Natologic/metalTravelPad/img/IMG_0876.jpg

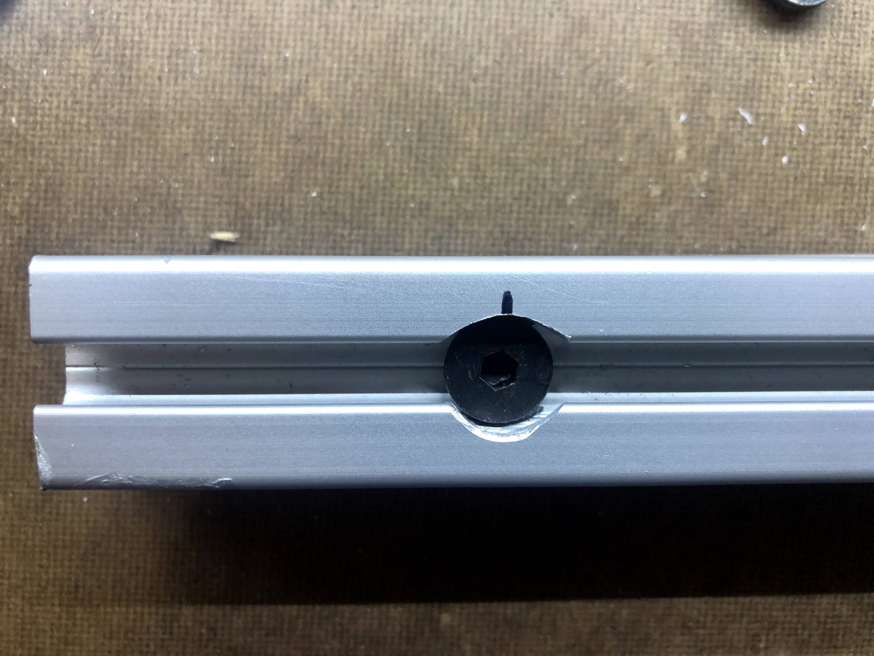
img/IMG_0876.jpg
